vankxr/usb-fanctl/software/mcu/src/include/adc.h

#ifndef __ADC_H__
#define __ADC_H__

#include <em_device.h>
#include "cmu.h"

#define ADC_5V0_DIV             2.219512195121951f // Voltage divider ratio
#define ADC_VEXT_DIV            11.f // Voltage divider ratio

#define ADC_5V0_CHAN            ADC_SINGLECTRL_POSSEL_APORT4XCH5
#define ADC_VEXT_CHAN           ADC_SINGLECTRL_POSSEL_APORT3XCH28

void adc_init();

float adc_get_avdd();
float adc_get_dvdd();
float adc_get_iovdd();
float adc_get_corevdd();
float adc_get_5v0();
float adc_get_vext();

float adc_get_temperature();

#endif  // __ADC_H__
